JuanGascaCalderon/Robot_Arm_4GDL/4GDL-Robot -Arm/Mechanical_Design_4GDL_Robot_Arm/Gripper/6dof_link1.SLDPRT

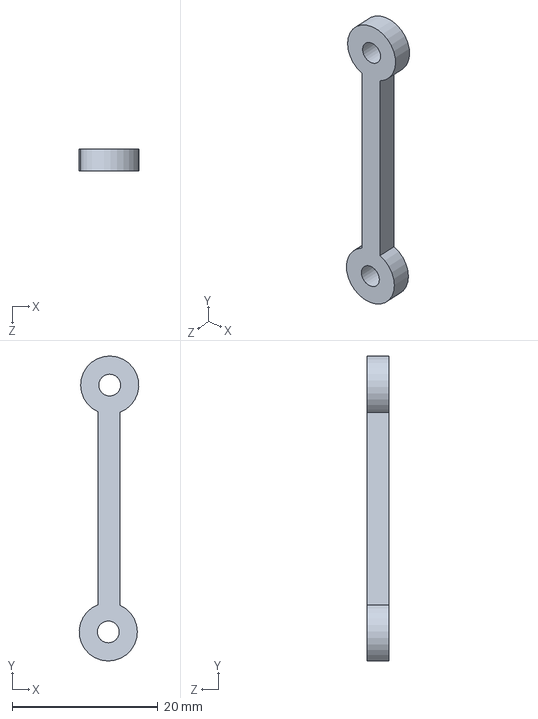
[picture p33: CAD file, 2024-03-17]
4GDL-Robot -Arm/Mechanical_Design_4GDL_Robot_Arm/Gripper/6dof_link1.SLDPRT
8.18 x 41.9 x 3.00 mm
