JuanGascaCalderon/Robot_Arm_4GDL/4GDL-Robot -Arm/Mechanical_Design_4GDL_Robot_Arm/Servo motor.SLDPRT

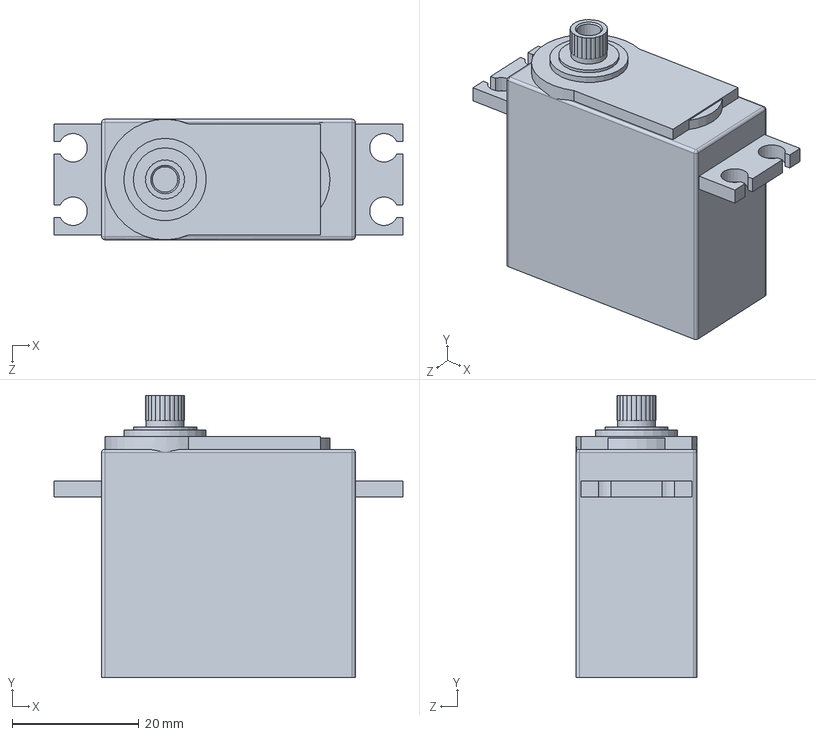
[picture p34: CAD file, 2024-03-17]
4GDL-Robot -Arm/Mechanical_Design_4GDL_Robot_Arm/Servo motor.SLDPRT
55.0 x 44.5 x 19.0 mm
