JuanGascaCalderon/Robot_Arm_4GDL/4GDL-Robot -Arm/Mechanical_Design_4GDL_Robot_Arm/Gripper/6dof_gear_link_small_hole.SLDPRT

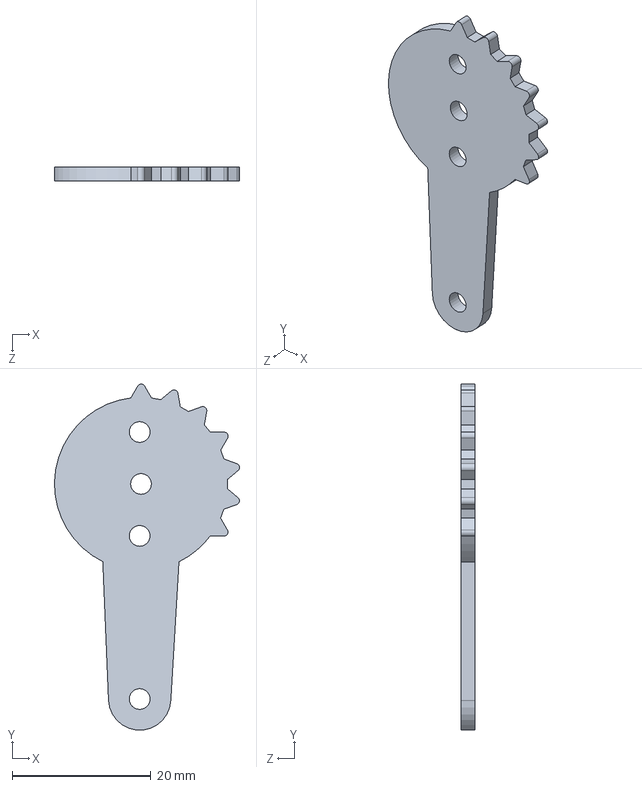
[picture p35: CAD file, 2024-03-17]
4GDL-Robot -Arm/Mechanical_Design_4GDL_Robot_Arm/Gripper/6dof_gear_link_small_hole.SLDPRT
26.7 x 50.0 x 2.00 mm
