JuanGascaCalderon/Robot_Arm_4GDL/4GDL-Robot -Arm/Mechanical_Design_4GDL_Robot_Arm/Gripper/6dof_cylinder.SLDPRT

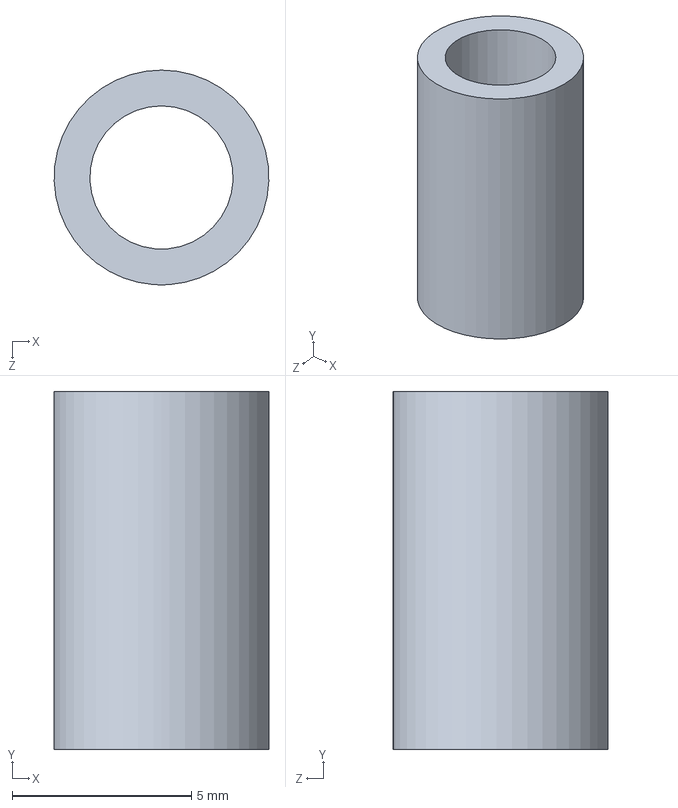
[picture p36: CAD file, 2024-03-17]
4GDL-Robot -Arm/Mechanical_Design_4GDL_Robot_Arm/Gripper/6dof_cylinder.SLDPRT
6.00 x 10.0 x 6.00 mm
